ltsul4/hallsenser-leverless-439/pcb/acrylic/元データ/1bottom_top/bottom1.pdf

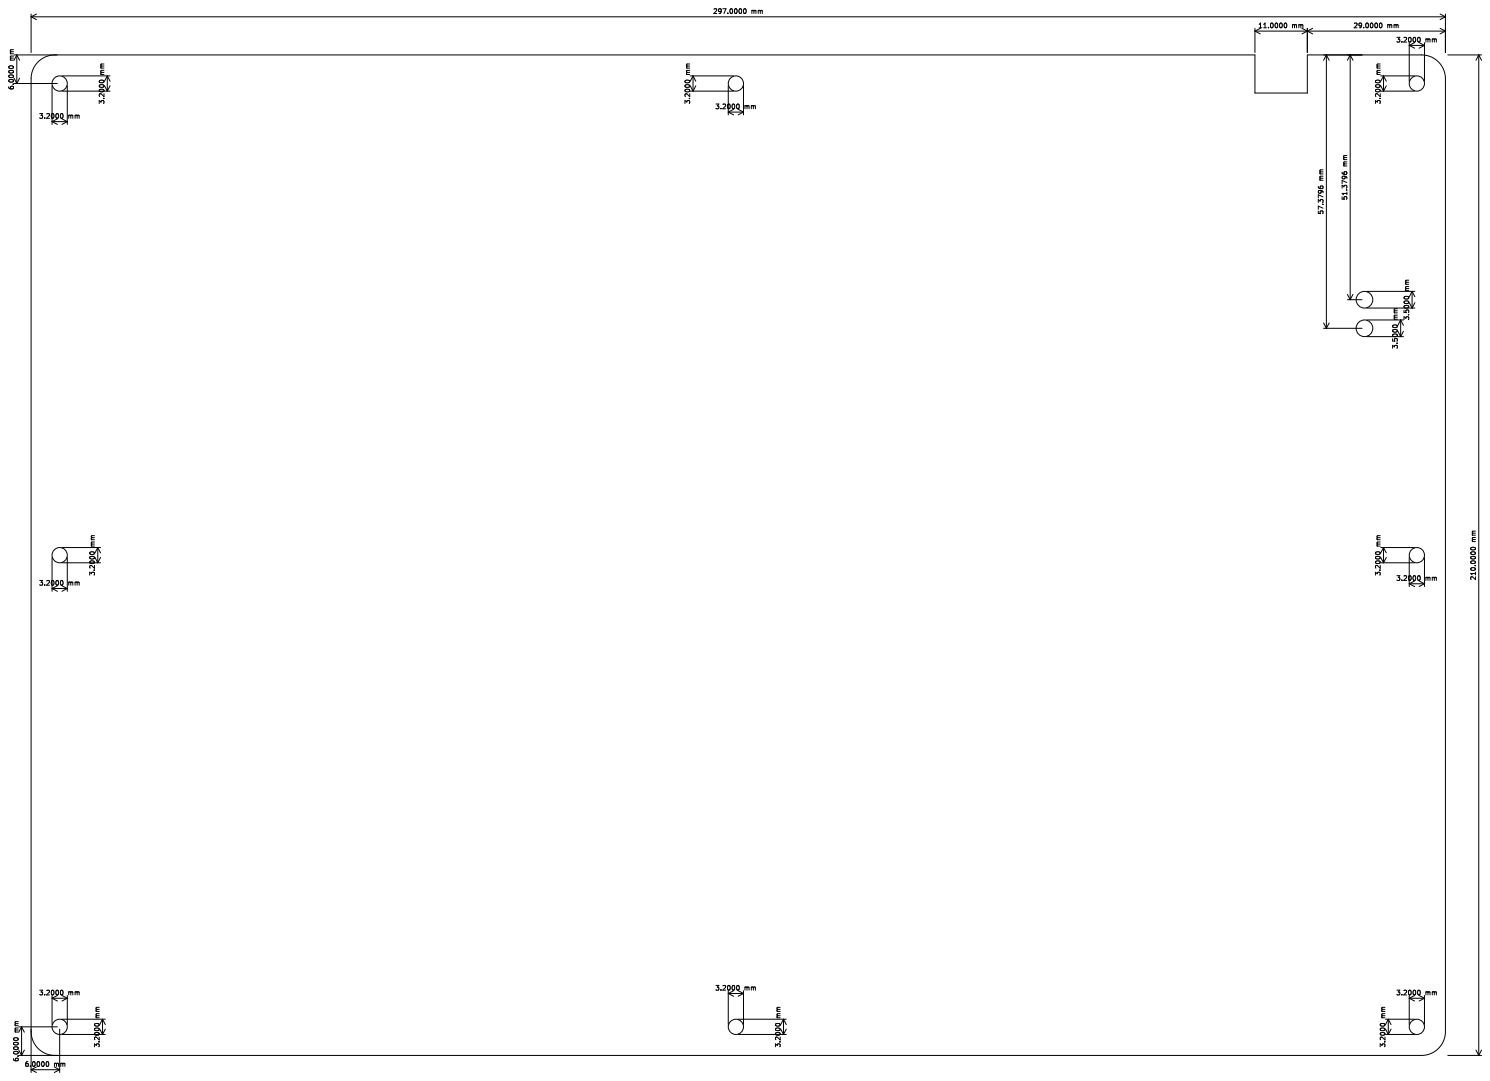
[picture p25: page 1]
