ltsul4/hallsenser-leverless-439/pcb/acrylic/元データ/1middle/middle.pdf

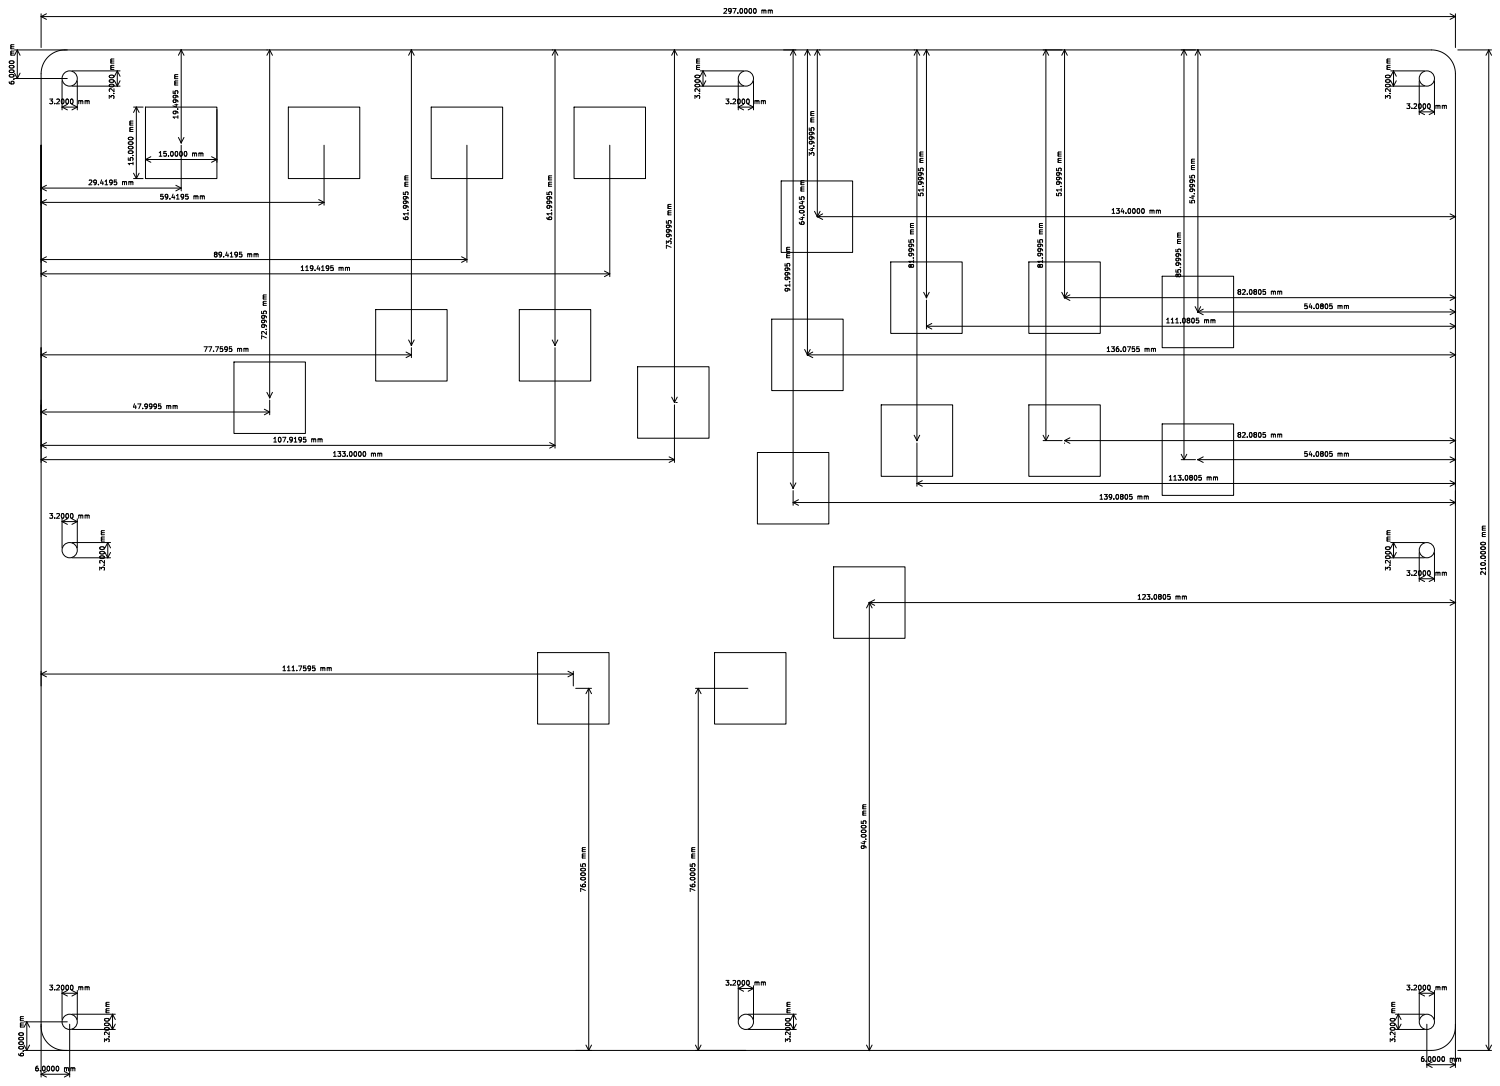
[picture p26: page 1]
