ltsul4/hallsenser-leverless-439/pcb/acrylic/元データ/1top1/top1.pdf

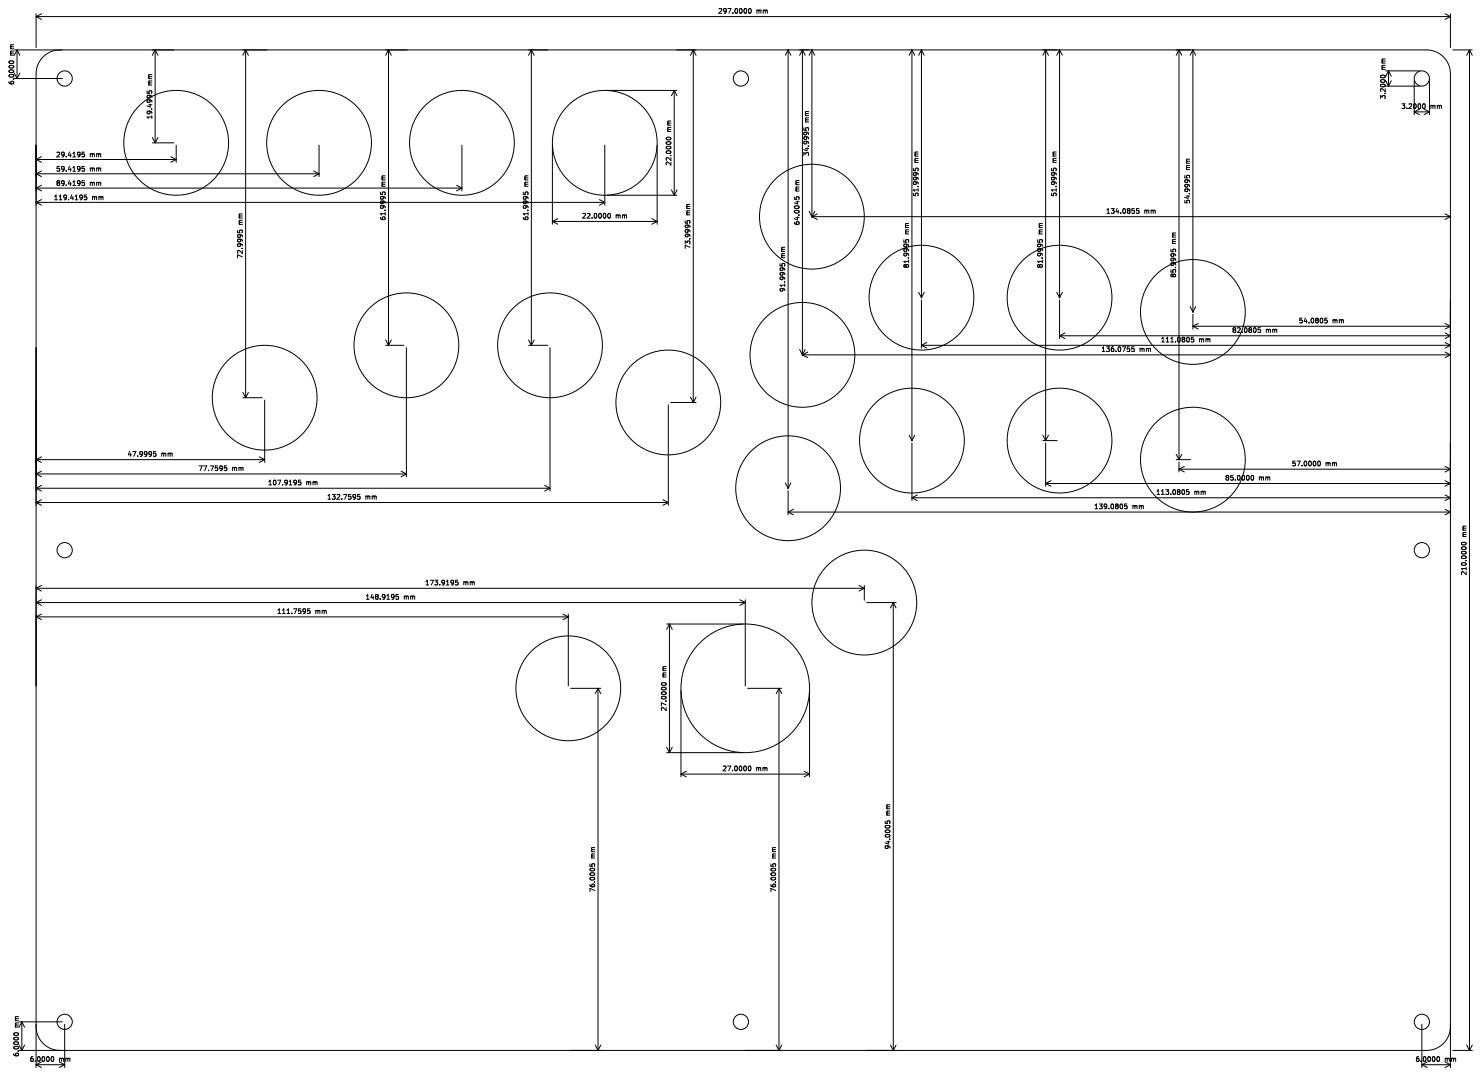
[picture p27: page 1]
