ltsul4/hallsenser-leverless-439/pcb/acrylic/元データ/1top2/top2.pdf

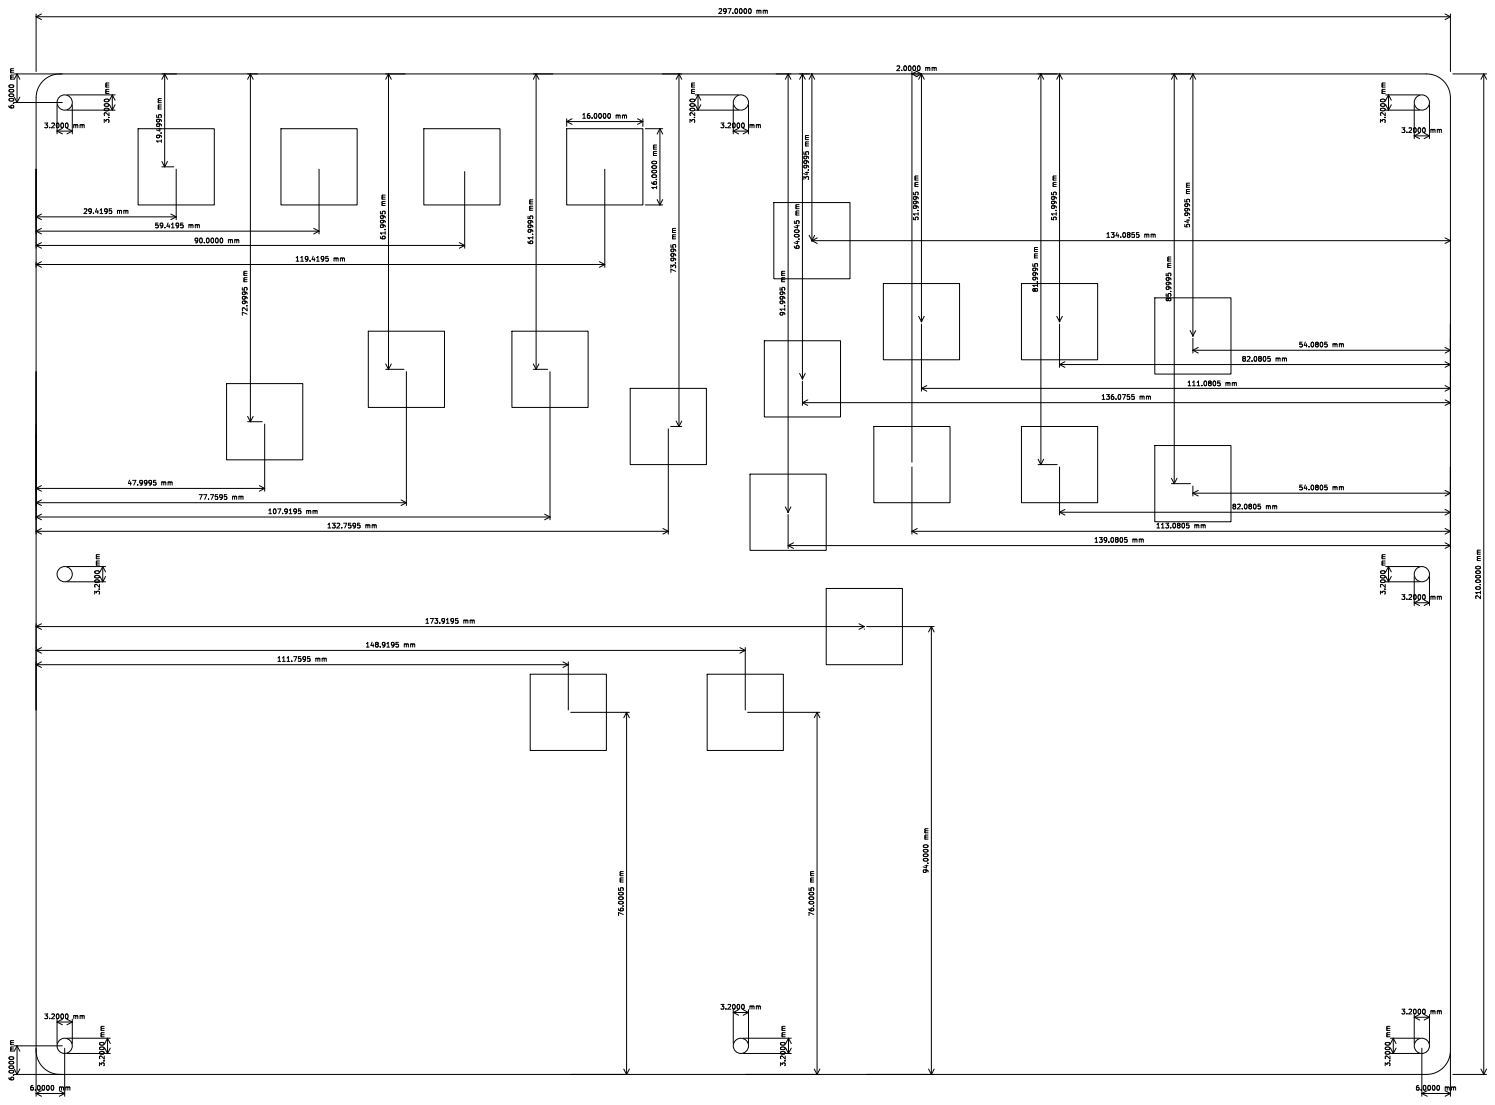
[picture p28: page 1]
