ltsul4/hallsenser-leverless-439/pcb/acrylic/元データ/kicad_bottom1/ember-Edge_Cuts.pdf

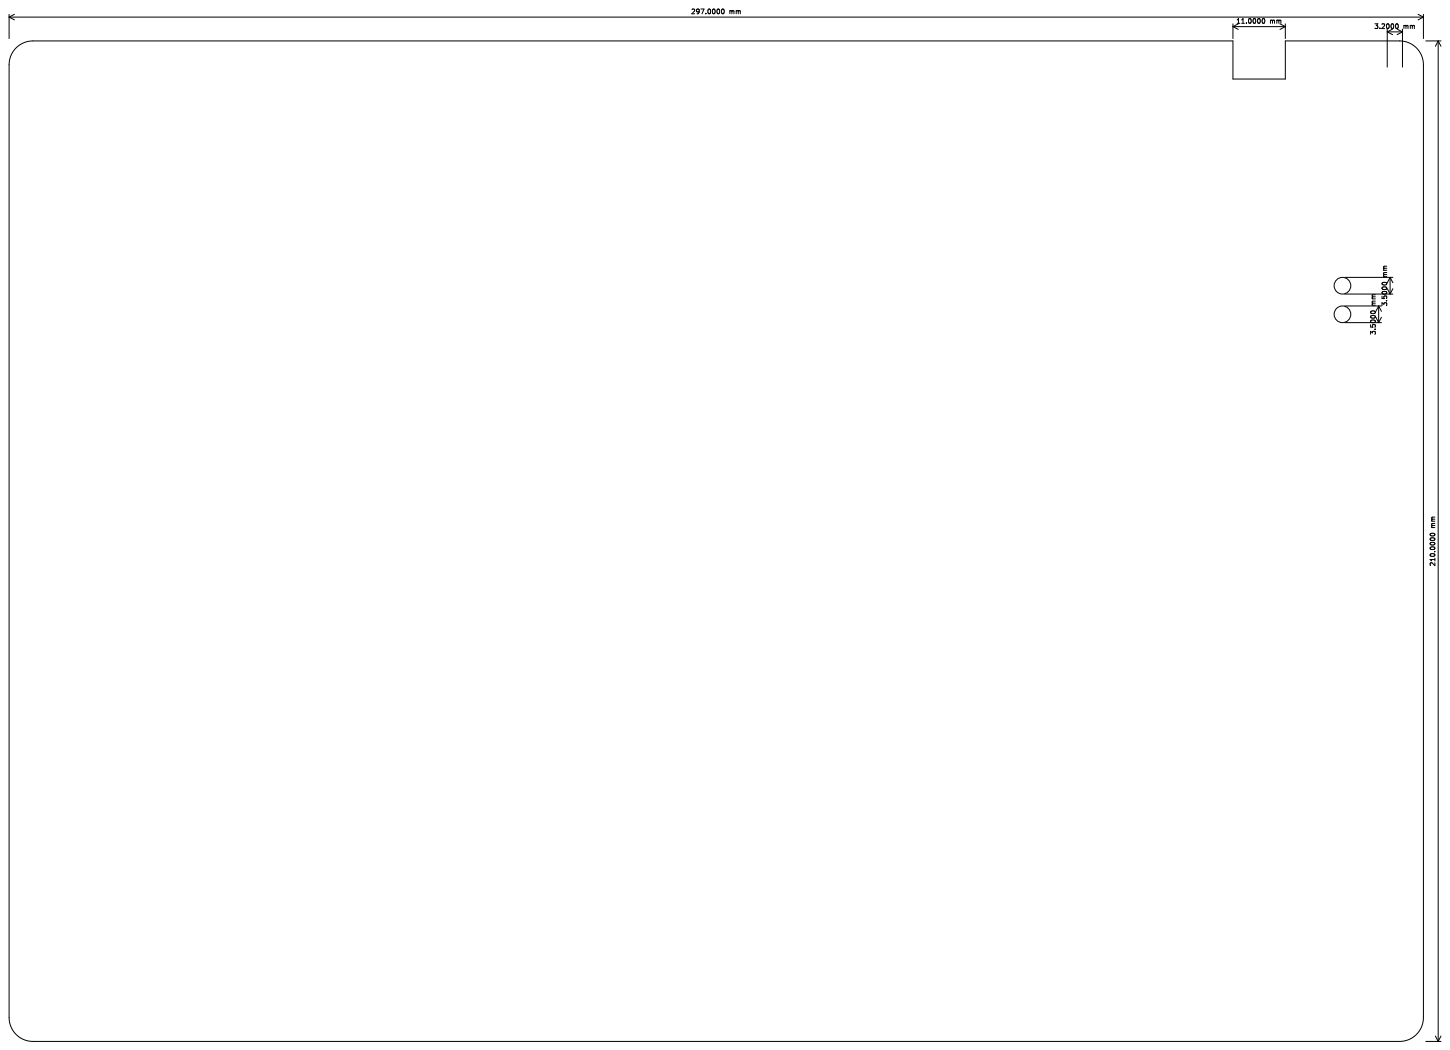
[picture p29: page 1]
