ltsul4/hallsenser-leverless-439/pcb/acrylic/元データ/kicad_bottom_2/bottom2.pdf

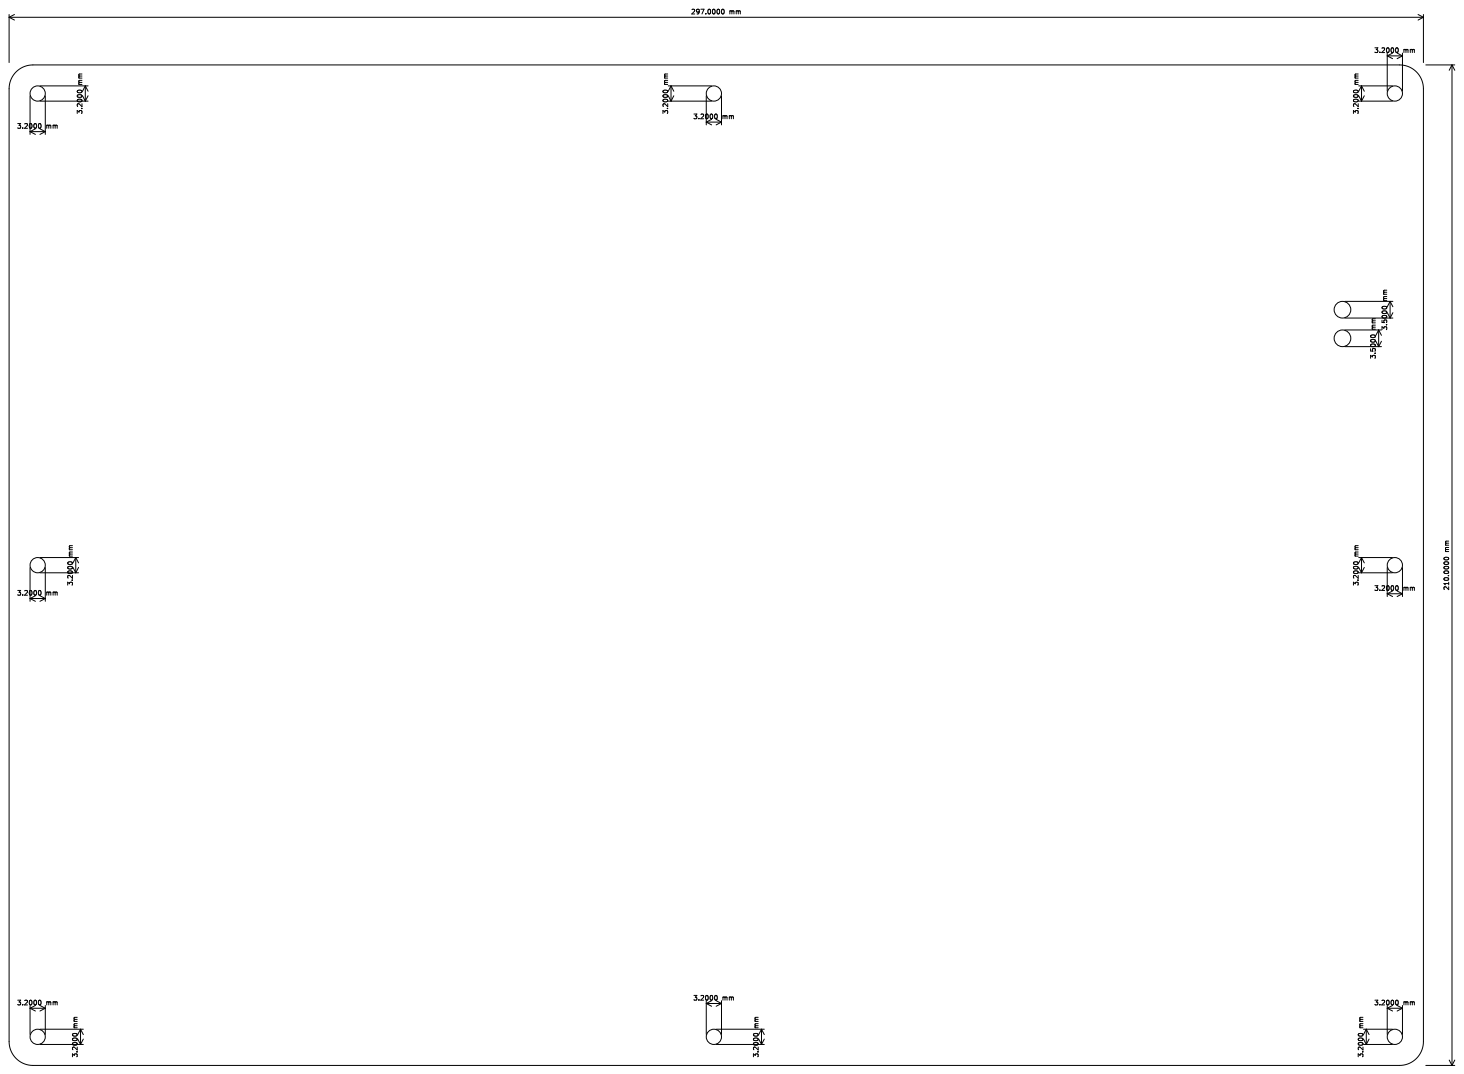
[picture p30: page 1]
