ltsul4/hallsenser-leverless-439/pcb/acrylic/元データ/kicad_bottom_2/ember-Edge_Cuts.pdf

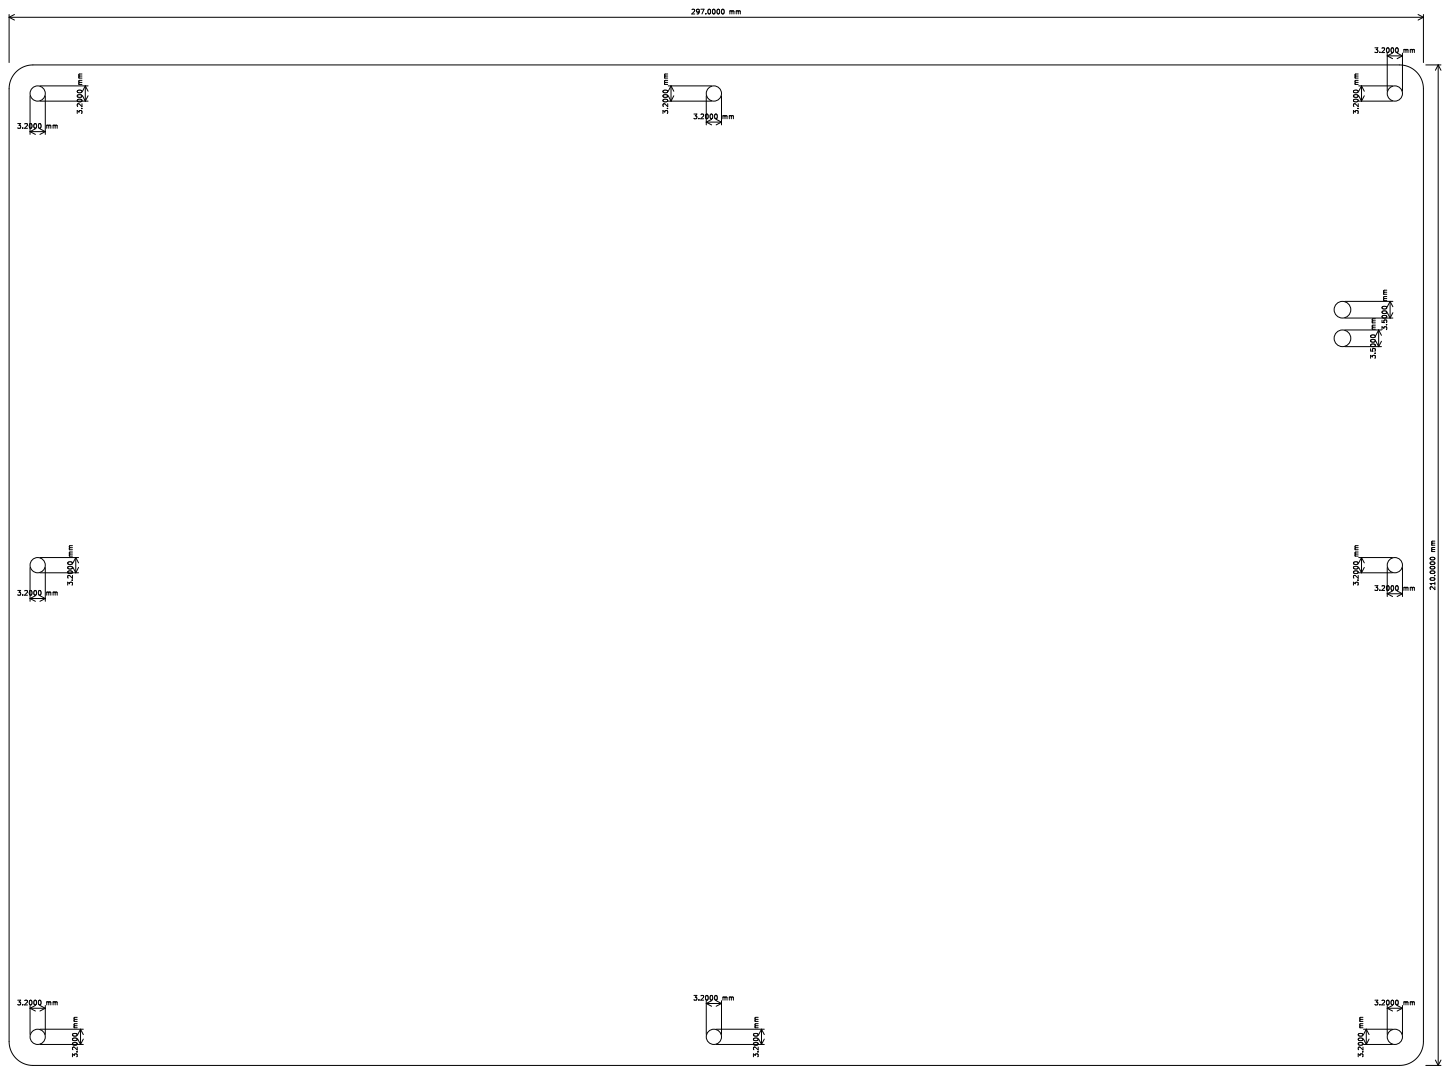
[picture p31: page 1]
